grafmar/BuildIndicator/src/BuildIndicator/BuildIndicator.h

#ifndef BUILDINDICATOR_H
#define BUILDINDICATOR_H

#define NUM_OF_PIXEL_ROWS   8
#define NUM_OF_PIXEL_COLS   2
#define NUM_OF_PIXELS       (NUM_OF_PIXEL_ROWS * NUM_OF_PIXEL_COLS)

#define LED_PIN     D2
#define OLED_SDA    D3
#define OLED_SCK    D4
#define OLED_RESET  D5

#define SCREEN_WIDTH 128 // OLED display width, in pixels
#define SCREEN_HEIGHT 64 // OLED display height, in pixels

#endif // BUILDINDICATOR_H
